viuhimciuc/Cartridge-NES/Discrete logic boards using/NES-AxROM/NES-AxROM.png

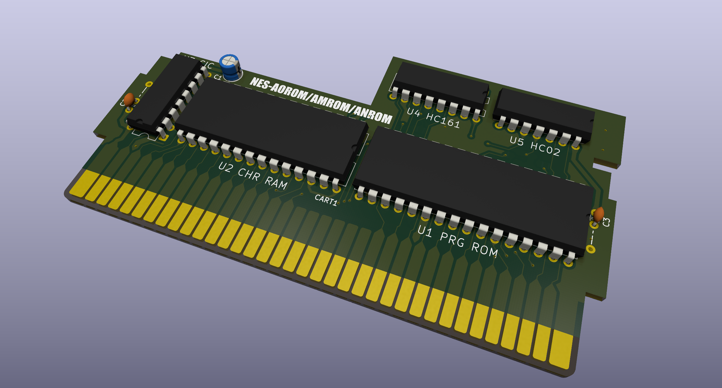
Discrete logic boards using/NES-AxROM/NES-AxROM.png
