viuhimciuc/Cartridge-NES/Discrete logic boards using/NES-UxROM/NES-UxROM.png

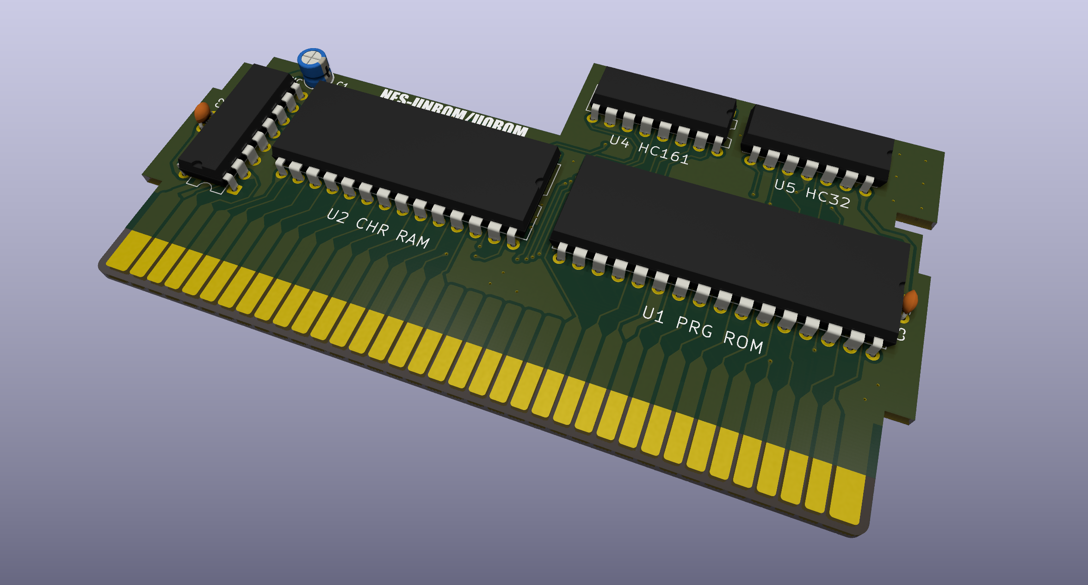
Discrete logic boards using/NES-UxROM/NES-UxROM.png
