viuhimciuc/Cartridge-NES/MMC1 boards NES-SxROM/NES-SLROM/NES-SLROM.png

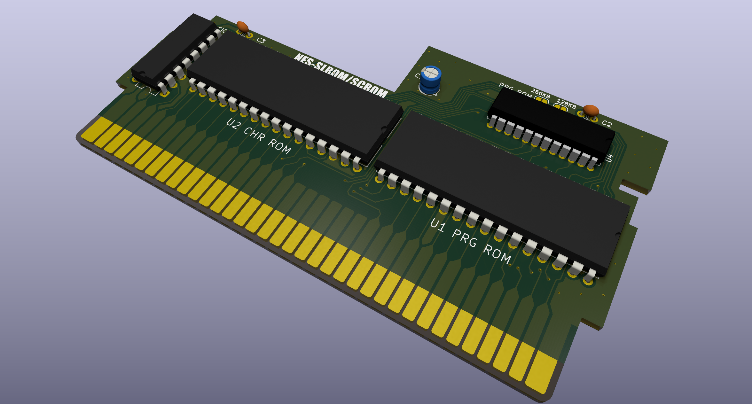
MMC1 boards NES-SxROM/NES-SLROM/NES-SLROM.png
