viuhimciuc/Cartridge-NES/MMC3 boards NES-TxROM/NES-TSROM/NES-TSROM.png

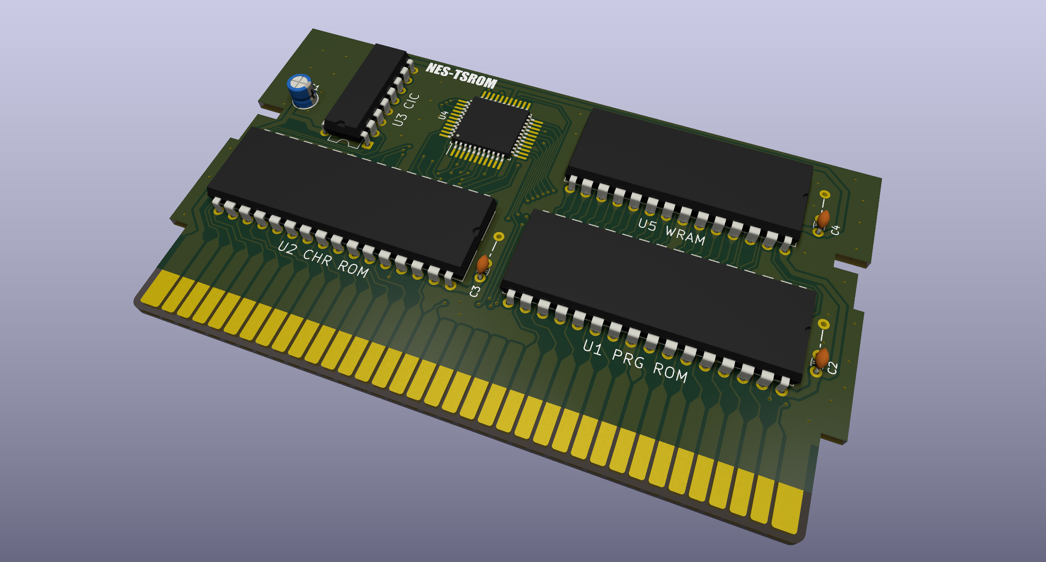
MMC3 boards NES-TxROM/NES-TSROM/NES-TSROM.png
