viuhimciuc/Cartridge-NES/NES MASK ROM/CHR_ROM/MASK_CHR_ROM_32KB_Half-Holes_Bottom_28pin/MASK_CHR_ROM_32KB_Half-Holes_Bottom_28pin.png

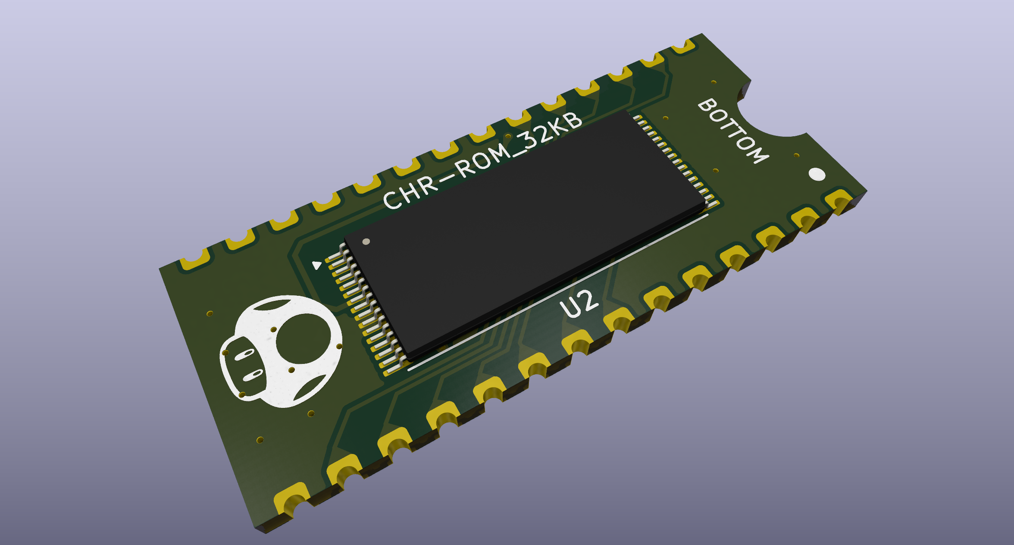
NES MASK ROM/CHR_ROM/MASK_CHR_ROM_32KB_Half-Holes_Bottom_28pin/MASK_CHR_ROM_32KB_Half-Holes_Bottom_28pin.png
