viuhimciuc/Cartridge-NES/MMC3 boards NES-TxROM/NES-TSROM/NES-TSROM.kicad_pcb

## KiCad design MMC3 boards NES-TxROM/NES-TSROM/NES-TSROM.kicad_pcb (2026-08-26)

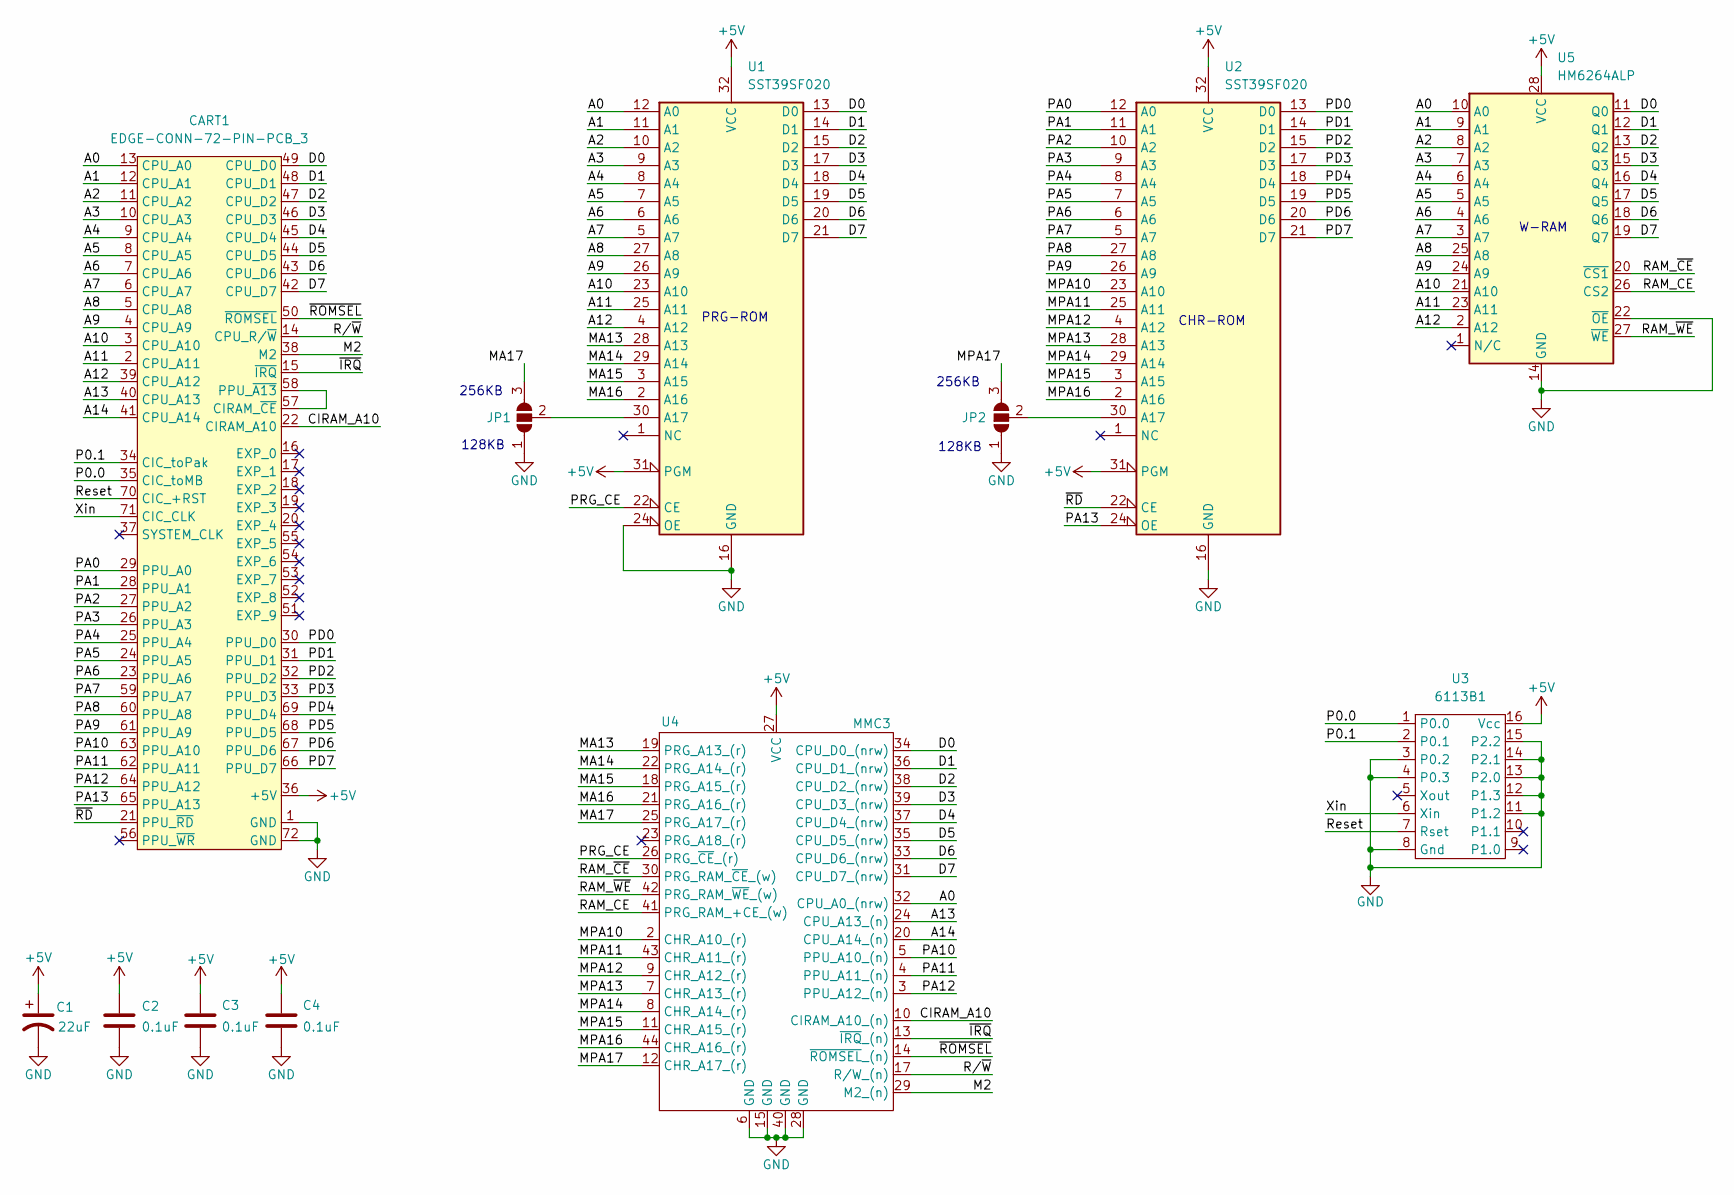
[picture p28: schematic NES-TSROM.kicad_sch]

Parts:
C1: 22uF; CP_Radial_D4.0mm_P2.00mm
C2, C3, C4: 0.1uF; C_Axial_P7.5mm_P2.50mm
CART1: EDGE-CONN-72-PIN-PCB_3; PCB_3-CART-72-2.50-CONN
JP1, JP2: SolderJumper_3_Open; SolderJumper-3_P1.3mm_Open_RoundedPad1.0x1.5mm_NumberLabels
U1, U2: SST39SF020; DIP-32_W15.24mm
U3: 6113B1; DIP-16_W7.62mm
U4: MMC3; MMC3_TQFP-44
U5: HM6264ALP; DIP-28_W15.24mm

Connections:
+5V: C1.1, C2.1, C3.1, C4.1, CART1.36 (+5V), U1.31 (PGM), U1.32 (VCC), U2.31 (PGM), U2.32 (VCC), U3.16 (Vcc), U4.27 (VCC), U5.28 (VCC)
/A0: CART1.13 (CPU_A0), U1.12 (A0), U4.32 (CPU_A0_(nrw)), U5.10 (A0)
/A1: CART1.12 (CPU_A1), U1.11 (A1), U5.9 (A1)
/A2: CART1.11 (CPU_A2), U1.10 (A2), U5.8 (A2)
/A3: CART1.10 (CPU_A3), U1.9 (A3), U5.7 (A3)
/A4: CART1.9 (CPU_A4), U1.8 (A4), U5.6 (A4)
/A5: CART1.8 (CPU_A5), U1.7 (A5), U5.5 (A5)
/A6: CART1.7 (CPU_A6), U1.6 (A6), U5.4 (A6)
/A7: CART1.6 (CPU_A7), U1.5 (A7), U5.3 (A7)
/A8: CART1.5 (CPU_A8), U1.27 (A8), U5.25 (A8)
/A9: CART1.4 (CPU_A9), U1.26 (A9), U5.24 (A9)
/A10: CART1.3 (CPU_A10), U1.23 (A10), U5.21 (A10)
/A11: CART1.2 (CPU_A11), U1.25 (A11), U5.23 (A11)
/A12: CART1.39 (CPU_A12), U1.4 (A12), U5.2 (A12)
/A13: CART1.40 (CPU_A13), U4.24 (CPU_A13_(n))
/A14: CART1.41 (CPU_A14), U4.20 (CPU_A14_(n))
/CIRAM_A10: CART1.22 (CIRAM_A10), U4.10 (CIRAM_A10_(n))
/D0: CART1.49 (CPU_D0), U1.13 (D0), U4.34 (CPU_D0_(nrw)), U5.11 (Q0)
/D1: CART1.48 (CPU_D1), U1.14 (D1), U4.36 (CPU_D1_(nrw)), U5.12 (Q1)
/D2: CART1.47 (CPU_D2), U1.15 (D2), U4.38 (CPU_D2_(nrw)), U5.13 (Q2)
/D3: CART1.46 (CPU_D3), U1.17 (D3), U4.39 (CPU_D3_(nrw)), U5.15 (Q3)
/D4: CART1.45 (CPU_D4), U1.18 (D4), U4.37 (CPU_D4_(nrw)), U5.16 (Q4)
/D5: CART1.44 (CPU_D5), U1.19 (D5), U4.35 (CPU_D5_(nrw)), U5.17 (Q5)
/D6: CART1.43 (CPU_D6), U1.20 (D6), U4.33 (CPU_D6_(nrw)), U5.18 (Q6)
/D7: CART1.42 (CPU_D7), U1.21 (D7), U4.31 (CPU_D7_(nrw)), U5.19 (Q7)
/M2: CART1.38 (M2), U4.29 (M2_(n))
/MA13: U1.28 (A13), U4.19 (PRG_A13_(r))
/MA14: U1.29 (A14), U4.22 (PRG_A14_(r))
/MA15: U1.3 (A15), U4.18 (PRG_A15_(r))
/MA16: U1.2 (A16), U4.21 (PRG_A16_(r))
/MA17: JP1.3 (B), U4.25 (PRG_A17_(r))
/MPA10: U2.23 (A10), U4.2 (CHR_A10_(r))
/MPA11: U2.25 (A11), U4.43 (CHR_A11_(r))
/MPA12: U2.4 (A12), U4.9 (CHR_A12_(r))
/MPA13: U2.28 (A13), U4.7 (CHR_A13_(r))
/MPA14: U2.29 (A14), U4.8 (CHR_A14_(r))
/MPA15: U2.3 (A15), U4.11 (CHR_A15_(r))
/MPA16: U2.2 (A16), U4.44 (CHR_A16_(r))
/MPA17: JP2.3 (B), U4.12 (CHR_A17_(r))
/P0.0: CART1.35 (CIC_toMB), U3.1 (P0.0)
/P0.1: CART1.34 (CIC_toPak), U3.2 (P0.1)
/PA0: CART1.29 (PPU_A0), U2.12 (A0)
/PA1: CART1.28 (PPU_A1), U2.11 (A1)
/PA2: CART1.27 (PPU_A2), U2.10 (A2)
/PA3: CART1.26 (PPU_A3), U2.9 (A3)
/PA4: CART1.25 (PPU_A4), U2.8 (A4)
/PA5: CART1.24 (PPU_A5), U2.7 (A5)
/PA6: CART1.23 (PPU_A6), U2.6 (A6)
/PA7: CART1.59 (PPU_A7), U2.5 (A7)
/PA8: CART1.60 (PPU_A8), U2.27 (A8)
/PA9: CART1.61 (PPU_A9), U2.26 (A9)
/PA10: CART1.63 (PPU_A10), U4.5 (PPU_A10_(n))
/PA11: CART1.62 (PPU_A11), U4.4 (PPU_A11_(n))
/PA12: CART1.64 (PPU_A12), U4.3 (PPU_A12_(n))
/PA13: CART1.65 (PPU_A13), U2.24 (OE)
/PD0: CART1.30 (PPU_D0), U2.13 (D0)
/PD1: CART1.31 (PPU_D1), U2.14 (D1)
/PD2: CART1.32 (PPU_D2), U2.15 (D2)
/PD3: CART1.33 (PPU_D3), U2.17 (D3)
/PD4: CART1.69 (PPU_D4), U2.18 (D4)
/PD5: CART1.68 (PPU_D5), U2.19 (D5)
/PD6: CART1.67 (PPU_D6), U2.20 (D6)
/PD7: CART1.66 (PPU_D7), U2.21 (D7)
/PRG_CE: U1.22 (CE), U4.26 (PRG_~CE_(r))
/RAM_CE: U4.41 (PRG_RAM_+CE_(w)), U5.26 (CS2)
/RAM_~CE: U4.30 (PRG_RAM_~CE_(w)), U5.20 (~CS1)
/RAM_~WE: U4.42 (PRG_RAM_~WE_(w)), U5.27 (~WE)
/Reset: CART1.70 (CIC_+RST), U3.7 (Rset)
/R/~W: CART1.14 (CPU_R/~W), U4.17 (R/W_(n))
/Xin: CART1.71 (CIC_CLK), U3.6 (Xin)
/~IRQ: CART1.15 (~IRQ), U4.13 (~IRQ_(n))
/~RD: CART1.21 (PPU_~RD), U2.22 (CE)
/~ROMSEL: CART1.50 (~ROMSEL), U4.14 (~ROMSEL_(n))
GND: C1.2, C2.2, C3.2, C4.2, CART1.1 (GND), CART1.72 (GND), JP1.1 (A), JP2.1 (A), U1.16 (GND), U1.24 (OE), U2.16 (GND), U3.3 (P0.2), U3.4 (P0.3), U3.8 (Gnd), U3.11 (P1.2), U3.12 (P1.3), U3.13 (P2.0), U3.14 (P2.1), U3.15 (P2.2), U4.6 (GND), U4.15 (GND), U4.28 (GND), U4.40 (GND), U5.14 (GND), U5.22 (~OE)
unnamed: CART1.57 (CIRAM_~CE), CART1.58 (PPU_~A13)
unnamed: JP1.2 (C), U1.30 (A17)
unnamed: JP2.2 (C), U2.30 (A17)

Notes on the sheet:
W-RAM
CHR-ROM
256KB
128KB
PRG-ROM
