viuhimciuc/Cartridge-NES/MMC3 boards NES-TxROM/NES-TSROM/NES-TSROM.kicad_pcb

## KiCad design MMC3 boards NES-TxROM/NES-TSROM/NES-TSROM.kicad_pcb (continued)

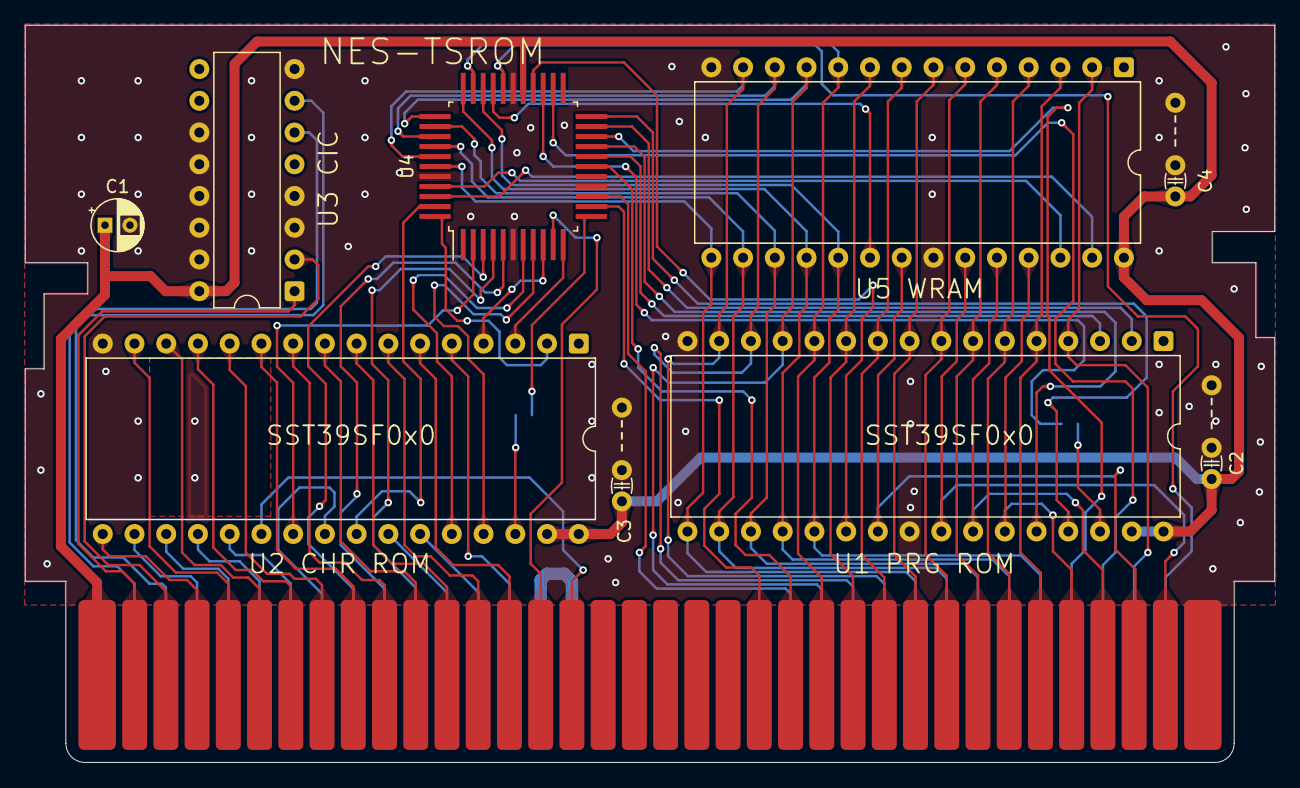
[picture p29: board NES-TSROM.kicad_pcb from above]

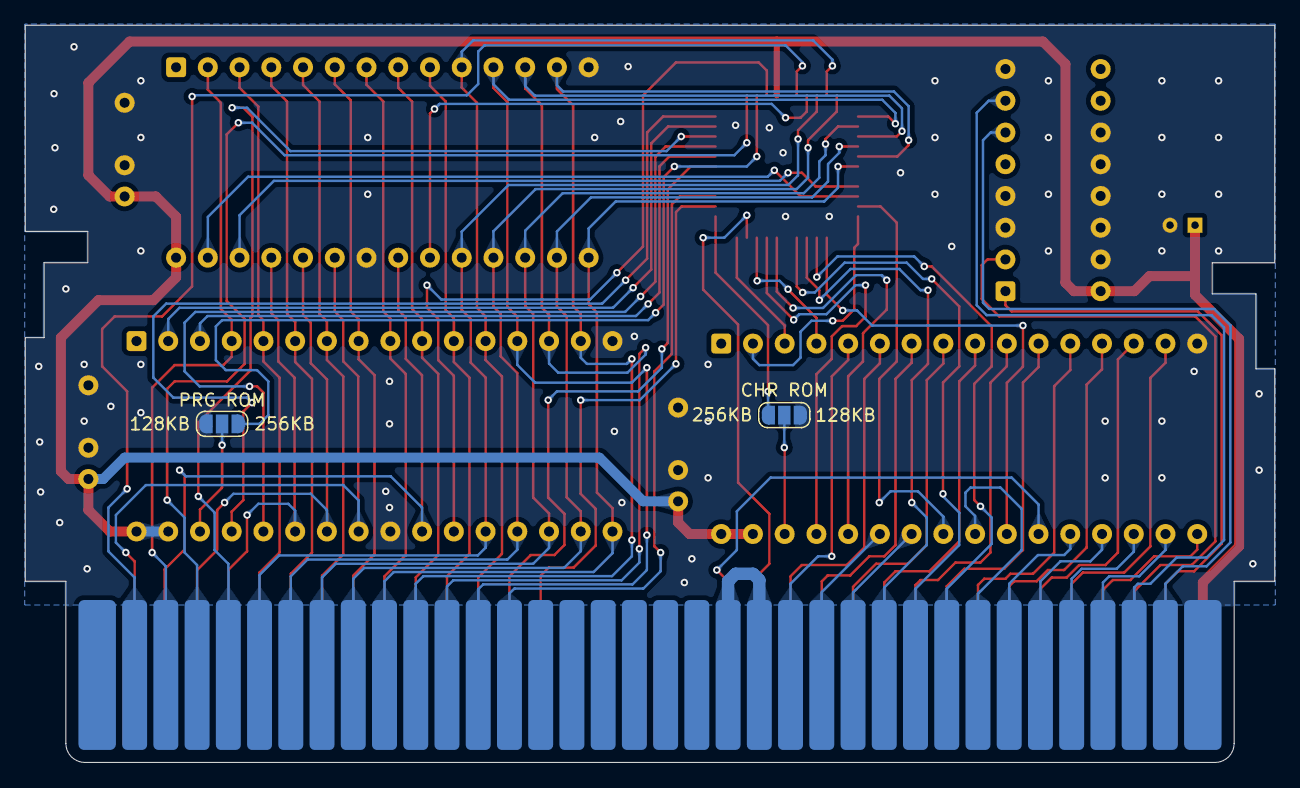
[picture p30: board NES-TSROM.kicad_pcb from below]

Board: 2 copper layers, 100.0 x 59.0 mm, 12 parts (2 on the bottom side), 77 nets.
