viuhimciuc/Cartridge-NES/MMC1 boards NES-SxROM/NES-SNROM/NES-SNROM.kicad_pcb

## KiCad design MMC1 boards NES-SxROM/NES-SNROM/NES-SNROM.kicad_pcb (2026-08-26)

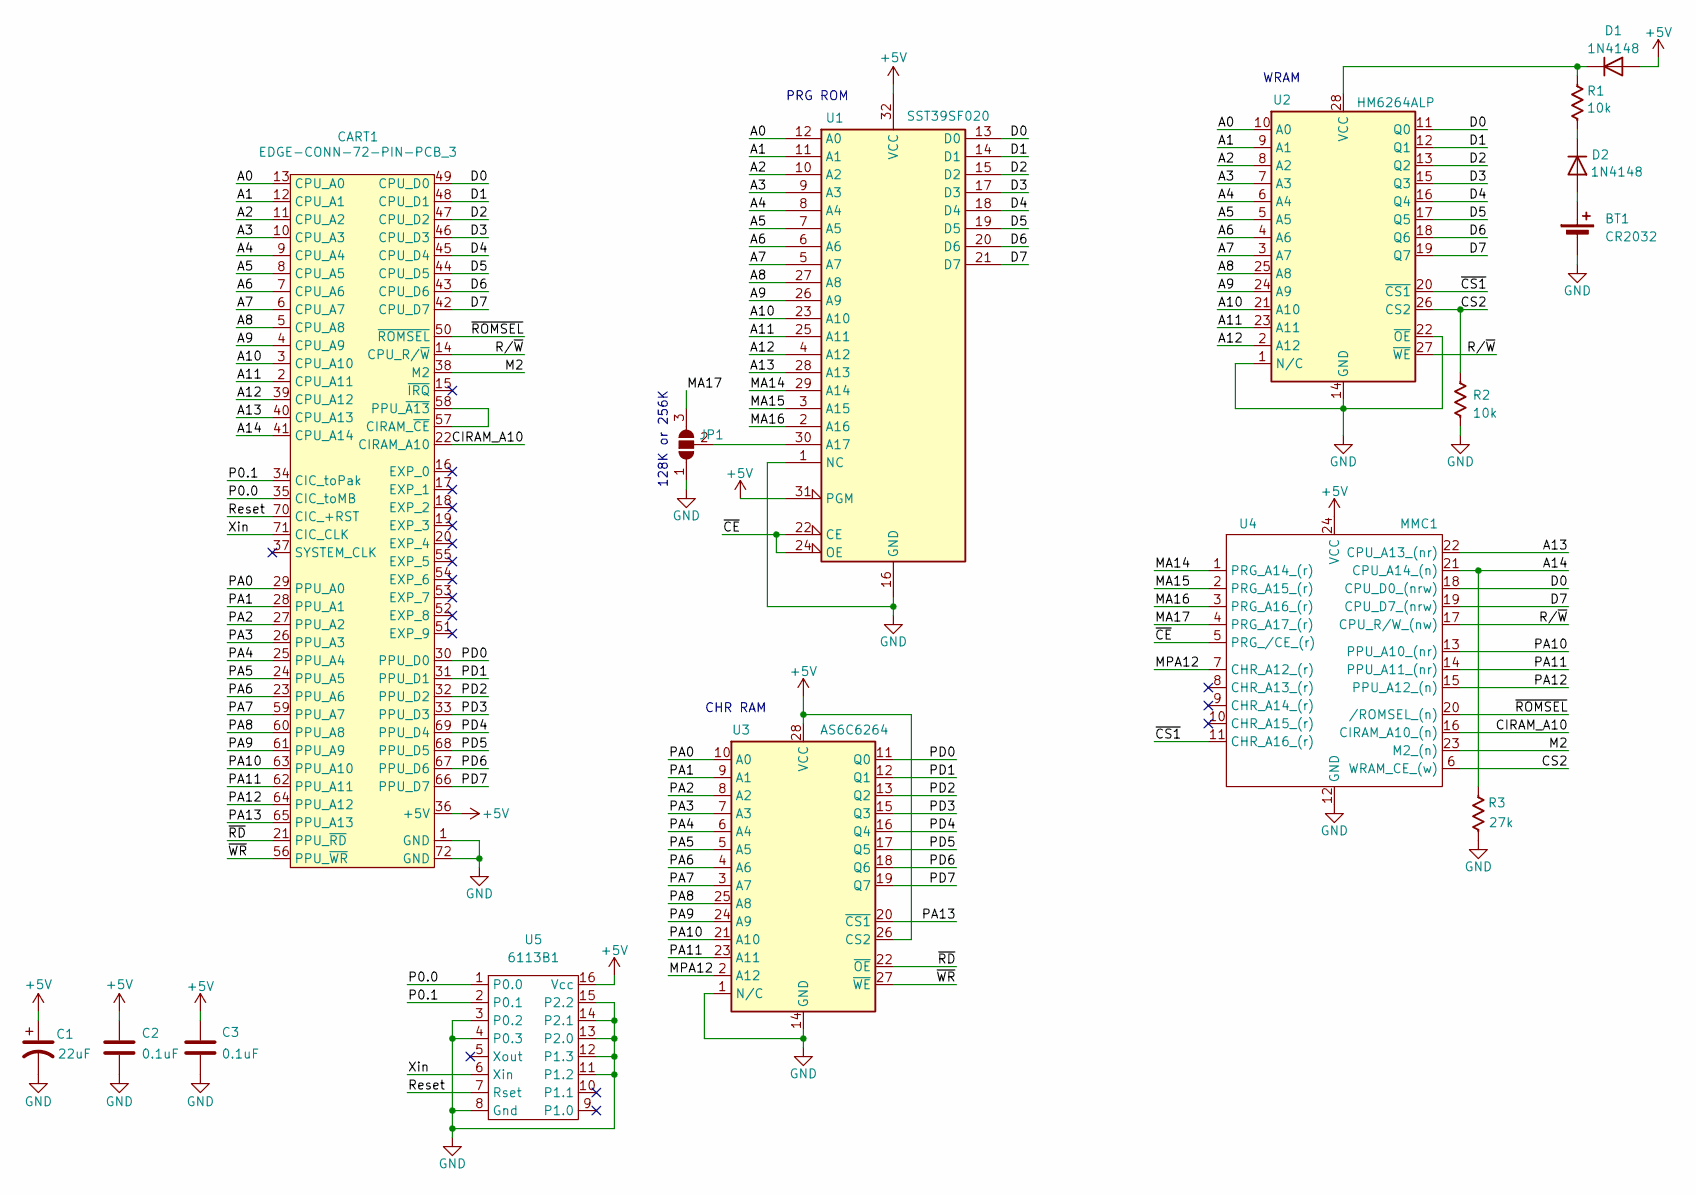
[picture p31: schematic NES-SNROM.kicad_sch]

Parts:
BT1: CR2032; Battery_Panasonic_CR2032-HFN_Horizontal_CircularHoles
C1: 22uF; CP_Radial_D4.0mm_P2.00mm
C2, C3: 0.1uF; C_Axial_P7.5mm_P2.50mm
CART1: EDGE-CONN-72-PIN-PCB_3; PCB_3-CART-72-2.50-CONN
D1, D2: 1N4148; D_DO-35_SOD27_P7.62mm_Horizontal
JP1: SolderJumper_3_Open; SolderJumper-3_P1.3mm_Open_RoundedPad1.0x1.5mm_NumberLabels
R1, R2: 10k; R_Axial_DIN0204_L3.6mm_D1.6mm_P5.08mm_Horizontal
R3: 27k; R_Axial_DIN0204_L3.6mm_D1.6mm_P5.08mm_Horizontal
U1: SST39SF020; DIP-32_W15.24mm
U2: HM6264ALP; DIP-28_W15.24mm
U3: AS6C6264; DIP-28_W15.24mm
U4: MMC1; DIP-24_W7.62mm_Pads_1.78mm
U5: 6113B1; DIP-16_W7.62mm

Connections:
+5V: C1.1, C2.1, C3.1, CART1.36 (+5V), D1.2 (A), U1.31 (PGM), U1.32 (VCC), U3.26 (CS2), U3.28 (VCC), U4.24 (VCC), U5.16 (Vcc)
/A0: CART1.13 (CPU_A0), U1.12 (A0), U2.10 (A0)
/A1: CART1.12 (CPU_A1), U1.11 (A1), U2.9 (A1)
/A2: CART1.11 (CPU_A2), U1.10 (A2), U2.8 (A2)
/A3: CART1.10 (CPU_A3), U1.9 (A3), U2.7 (A3)
/A4: CART1.9 (CPU_A4), U1.8 (A4), U2.6 (A4)
/A5: CART1.8 (CPU_A5), U1.7 (A5), U2.5 (A5)
/A6: CART1.7 (CPU_A6), U1.6 (A6), U2.4 (A6)
/A7: CART1.6 (CPU_A7), U1.5 (A7), U2.3 (A7)
/A8: CART1.5 (CPU_A8), U1.27 (A8), U2.25 (A8)
/A9: CART1.4 (CPU_A9), U1.26 (A9), U2.24 (A9)
/A10: CART1.3 (CPU_A10), U1.23 (A10), U2.21 (A10)
/A11: CART1.2 (CPU_A11), U1.25 (A11), U2.23 (A11)
/A12: CART1.39 (CPU_A12), U1.4 (A12), U2.2 (A12)
/A13: CART1.40 (CPU_A13), U1.28 (A13), U4.22 (CPU_A13_(nr))
/A14: CART1.41 (CPU_A14), R3.1, U4.21 (CPU_A14_(n))
/CIRAM_A10: CART1.22 (CIRAM_A10), U4.16 (CIRAM_A10_(n))
/CS2: R2.1, U2.26 (CS2), U4.6 (WRAM_CE_(w))
/D0: CART1.49 (CPU_D0), U1.13 (D0), U2.11 (Q0), U4.18 (CPU_D0_(nrw))
/D1: CART1.48 (CPU_D1), U1.14 (D1), U2.12 (Q1)
/D2: CART1.47 (CPU_D2), U1.15 (D2), U2.13 (Q2)
/D3: CART1.46 (CPU_D3), U1.17 (D3), U2.15 (Q3)
/D4: CART1.45 (CPU_D4), U1.18 (D4), U2.16 (Q4)
/D5: CART1.44 (CPU_D5), U1.19 (D5), U2.17 (Q5)
/D6: CART1.43 (CPU_D6), U1.20 (D6), U2.18 (Q6)
/D7: CART1.42 (CPU_D7), U1.21 (D7), U2.19 (Q7), U4.19 (CPU_D7_(nrw))
/M2: CART1.38 (M2), U4.23 (M2_(n))
/MA14: U1.29 (A14), U4.1 (PRG_A14_(r))
/MA15: U1.3 (A15), U4.2 (PRG_A15_(r))
/MA16: U1.2 (A16), U4.3 (PRG_A16_(r))
/MA17: JP1.3 (B), U4.4 (PRG_A17_(r))
/MPA12: U3.2 (A12), U4.7 (CHR_A12_(r))
/P0.0: CART1.35 (CIC_toMB), U5.1 (P0.0)
/P0.1: CART1.34 (CIC_toPak), U5.2 (P0.1)
/PA0: CART1.29 (PPU_A0), U3.10 (A0)
/PA1: CART1.28 (PPU_A1), U3.9 (A1)
/PA2: CART1.27 (PPU_A2), U3.8 (A2)
/PA3: CART1.26 (PPU_A3), U3.7 (A3)
/PA4: CART1.25 (PPU_A4), U3.6 (A4)
/PA5: CART1.24 (PPU_A5), U3.5 (A5)
/PA6: CART1.23 (PPU_A6), U3.4 (A6)
/PA7: CART1.59 (PPU_A7), U3.3 (A7)
/PA8: CART1.60 (PPU_A8), U3.25 (A8)
/PA9: CART1.61 (PPU_A9), U3.24 (A9)
/PA10: CART1.63 (PPU_A10), U3.21 (A10), U4.13 (PPU_A10_(nr))
/PA11: CART1.62 (PPU_A11), U3.23 (A11), U4.14 (PPU_A11_(nr))
/PA12: CART1.64 (PPU_A12), U4.15 (PPU_A12_(n))
/PA13: CART1.65 (PPU_A13), U3.20 (~CS1)
/PD0: CART1.30 (PPU_D0), U3.11 (Q0)
/PD1: CART1.31 (PPU_D1), U3.12 (Q1)
/PD2: CART1.32 (PPU_D2), U3.13 (Q2)
/PD3: CART1.33 (PPU_D3), U3.15 (Q3)
/PD4: CART1.69 (PPU_D4), U3.16 (Q4)
/PD5: CART1.68 (PPU_D5), U3.17 (Q5)
/PD6: CART1.67 (PPU_D6), U3.18 (Q6)
/PD7: CART1.66 (PPU_D7), U3.19 (Q7)
/Reset: CART1.70 (CIC_+RST), U5.7 (Rset)
/R/~W: CART1.14 (CPU_R/~W), U2.27 (~WE), U4.17 (CPU_R/W_(nw))
/Xin: CART1.71 (CIC_CLK), U5.6 (Xin)
/~CE: U1.22 (CE), U1.24 (OE), U4.5 (PRG_/CE_(r))
/~CS1: U2.20 (~CS1), U4.11 (CHR_A16_(r))
/~RD: CART1.21 (PPU_~RD), U3.22 (~OE)
/~ROMSEL: CART1.50 (~ROMSEL), U4.20 (/ROMSEL_(n))
/~WR: CART1.56 (PPU_~WR), U3.27 (~WE)
GND: BT1.2 (-), C1.2, C2.2, C3.2, CART1.1 (GND), CART1.72 (GND), JP1.1 (A), R2.2, R3.2, U1.1 (NC), U1.16 (GND), U2.1 (N/C), U2.14 (GND), U2.22 (~OE), U3.1 (N/C), U3.14 (GND), U4.12 (GND), U5.3 (P0.2), U5.4 (P0.3), U5.8 (Gnd), U5.11 (P1.2), U5.12 (P1.3), U5.13 (P2.0), U5.14 (P2.1), U5.15 (P2.2)
unnamed: BT1.1 (+), D2.2 (A)
unnamed: CART1.57 (CIRAM_~CE), CART1.58 (PPU_~A13)
unnamed: D1.1 (K), R1.1, U2.28 (VCC)
unnamed: D2.1 (K), R1.2
unnamed: JP1.2 (C), U1.30 (A17)

Notes on the sheet:
PRG ROM
WRAM
128K or 256K
CHR RAM

Board: 2 copper layers, 16 parts (1 on the bottom side), 70 nets, no tracks yet.
